JasensCustoms/TheFrame-Layouts/SP26M Layout/JasensCustoms-TheFrame-SP26M-Outer.DXF

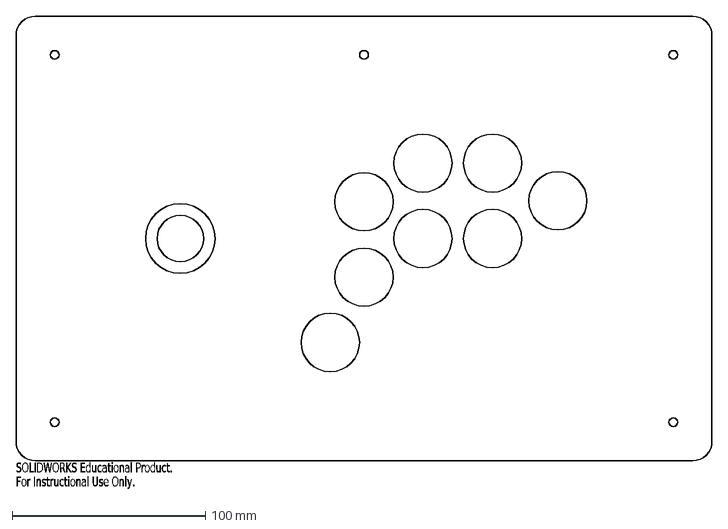
[picture p20: CAD file, 2025-01-15]
SP26M Layout/JasensCustoms-TheFrame-SP26M-Outer.DXF
SOLIDWORKS Educational Product.
For Instructional Use Only.
