JasensCustoms/TheFrame-Layouts/Taito Vewlix with Extra Buttons, 100mm Wide/JasensCustoms-TheFrame-TaitoVewlix Base - 100mm-Wide - Top 1.5mm.DXF

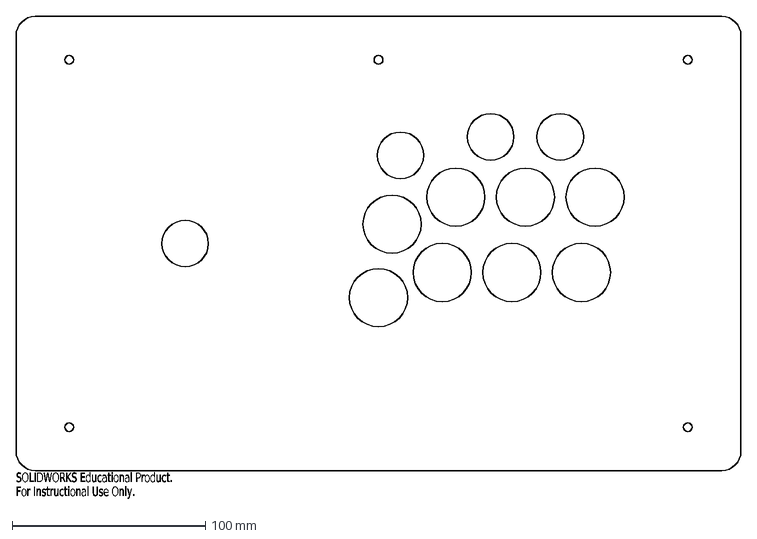
[picture p21: CAD file, 2024-09-08]
Taito Vewlix with Extra Buttons, 100mm Wide/JasensCustoms-TheFrame-TaitoVewlix Base - 100mm-Wide - Top 1.5mm.DXF
SOLIDWORKS Educational Product.
For Instructional Use Only.
