JasensCustoms/TheFrame-Layouts/Sega 2P Impact Custom/2919 - Robert B - Layout OUTER.dxf

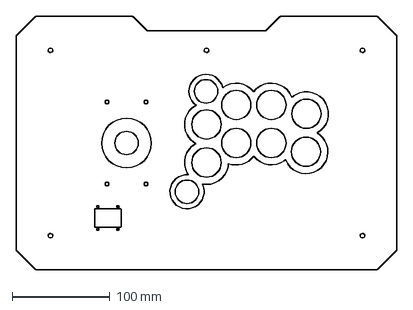
[picture p23: CAD file, 2025-08-12]
Sega 2P Impact Custom/2919 - Robert B - Layout OUTER.dxf
390.0 x 260.0 mm
