JasensCustoms/TheFrame-Layouts/Base Design Docs/TheFrame-Front-Neutrik Surrounded.dxf

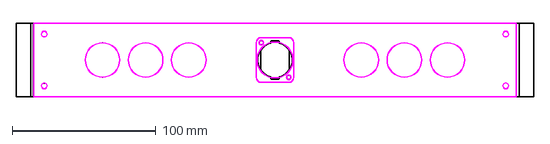
[picture p25: CAD file, 2024-09-15]
Base Design Docs/TheFrame-Front-Neutrik Surrounded.dxf
360.0 x 51.0 mm
