JasensCustoms/TheFrame-Layouts/Taito Vewlix with Extra Buttons, 100mm Wide/JasensCustoms-TheFrame-TaitoVewlix Base - 100mm-Wide - Bottom 5.6mm.DXF

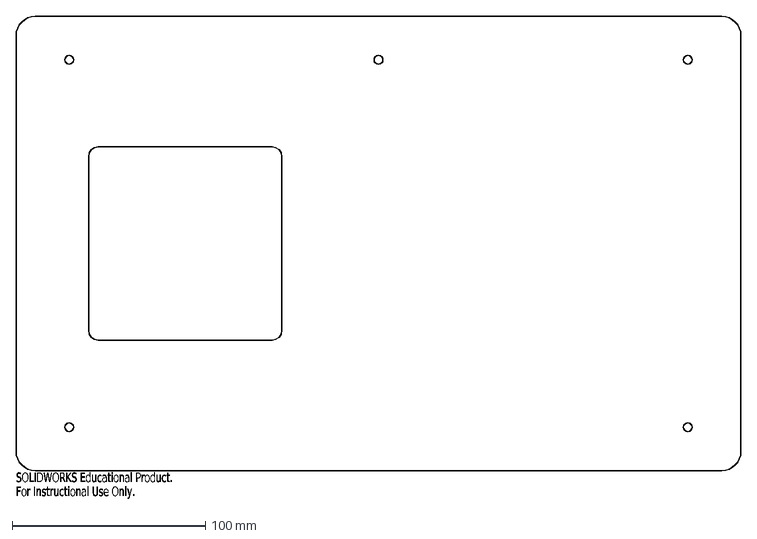
[picture p26: CAD file, 2024-09-08]
Taito Vewlix with Extra Buttons, 100mm Wide/JasensCustoms-TheFrame-TaitoVewlix Base - 100mm-Wide - Bottom 5.6mm.DXF
SOLIDWORKS Educational Product.
For Instructional Use Only.
