JasensCustoms/TheFrame-Layouts/Base Design Docs/TheFrame-Top Area.dxf

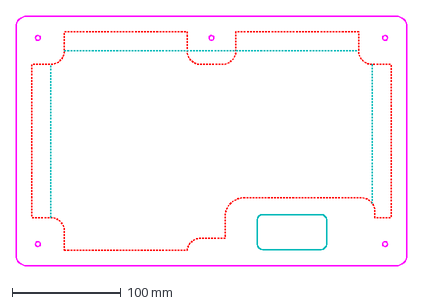
[picture p27: CAD file, 2024-09-15]
Base Design Docs/TheFrame-Top Area.dxf
360.0 x 230.0 mm
