JasensCustoms/TheFrame-Layouts/Base Design Docs/TheFrame-Bottom Area.dxf

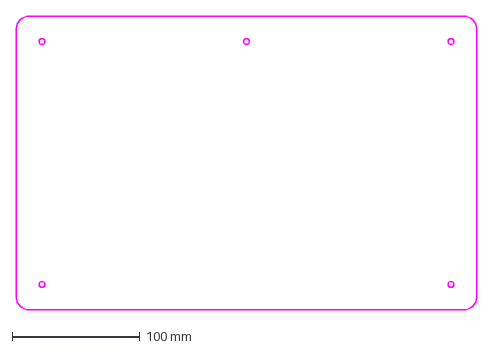
[picture p28: CAD file, 2024-09-15]
Base Design Docs/TheFrame-Bottom Area.dxf
360.0 x 230.0 mm
